joniburn/raspi-musicbox/python-musicbox/musicbox/score.py

# スコアファイル

import re
from datetime import datetime, timedelta
from typing import List, Tuple

from musicbox.scale import PITCH_FREQ_MAP


def _is_comment_line(line: str) -> bool:
    """コメント行であればTrueを返す。"""
    return line.startswith('#')


class ScoreParseError(Exception):
    """スコアファイルのパース失敗エラー"""
    def __init__(self, msg):
        super().__init__(msg)


class Note:
    """音階や長さを持った1つの音"""

    def __init__(self, note_line: str):
        cmd_args = re.split('[ ]+', note_line)
        self.pitch = cmd_args[0]       # 音階
        self.step = int(cmd_args[1])   # 音長基準(何分音符か)
        self.nstep = int(cmd_args[2])  # 音長(step何個分か)
        if len(cmd_args) <= 3:
            self.duration = 100        # 音の伸ばし率(何%まで伸ばすか)
        else:
            self.duration = int(cmd_args[3])
        if self.duration <= 0 or self.duration > 100:
            raise ScoreParseError(f'duration value should be in range '
                                  f'(0, 100]: {self.duration}')

    def to_timeline(self, bar: float, t: datetime):
        if self.pitch == 'x':
            freq = 0  # 休符
        else:
            freq = PITCH_FREQ_MAP[self.pitch]

        notelen = bar / self.step
        # N倍する前に、マイクロ秒以下を切り捨てる
        # このようにしないと、"x 16 1"を10行分と"x 8 5"を1行分にずれが生じる
        notelen = int(notelen * 1000000) / 1000000.0
        notelen = notelen * self.nstep

        if self.duration == 100:
            return [(freq, t + timedelta(seconds=notelen))]
        else:
            timeline = []
            notelen_on = notelen * self.duration / 100
            timeline.append((freq, t + timedelta(seconds=notelen_on)))
            timeline.append((0, t + timedelta(seconds=notelen)))
            return timeline


class ScoreBlock:
    """一定のBPMを持ったスコアのブロック"""

    def __init__(self, lines: List[str], ntrack: int):
        self._bpm = 0
        self._tracks = []
        for i in range(0, ntrack):
            self._tracks.append([])
        self._parse(lines)

    def _parse(self, lines: List[str]):
        for lnum, line in enumerate(lines):
            # 1行目はbpm行 "@ bpm XXX"
            if lnum == 0:
                self._parse_bpm(line)
                continue

            # コメント行と空行はスキップ
            if _is_comment_line(line) or not line:
                continue

            # 各トラックをパース
            track_lines = line.split(',')
            for i in range(0, len(self._tracks)):
                if len(track_lines) > i:
                    track_line = track_lines[i]
                else:
                    track_line = ''
                track_line = track_line.strip()
                if track_line:
                    self._tracks[i].append(Note(track_line))

    def _parse_bpm(self, bpm_line: str):
        bpm_line = bpm_line.split(',', maxsplit=1)[0]
        bpm_line_args = bpm_line.split(' ')
        if bpm_line_args[1] != 'bpm':
            raise ScoreParseError('no bpm line is provided at beggining '
                                  'of score block.')
        self._bpm = int(bpm_line_args[2])

    def build_timeline(self, start: datetime, track: int) \
            -> List[Tuple[float, datetime]]:
        # bpmから各音符の長さを計算
        bar = 60.0 / self._bpm * 4  # 1小節の長さ。4分音符はこの長さの1/4, ...

        timeline = []
        cur = start
        for note in self._tracks[track]:
            items = note.to_timeline(bar, cur)
            timeline.extend(items)
            cur = items[-1][1]
        return timeline


class TrackProperties:
    """トラック毎のプロパティ"""

    def __init__(self, mode='tone', duty=None):
        self.mode = mode
        self.duty = duty


class Score:
    """スコアファイルのパース結果を保持するクラス"""

    def __init__(self, fname):
        self.ntrack = 0
        self._track_props = []
        self._score_blocks = []
        self._parse(fname)

    def _parse(self, fname):
        # プロパティセクションとスコア本体の行を読み込む
        prop_lines = []
        score_blocks = []
        with open(fname) as f:
            # プロパティセクション
            for line in f:
                line = line.strip()
                if line.startswith('@'):
                    score_blocks.append([line])
                    break
                prop_lines.append(line)

            # スコア本体
            current_block_lines = score_blocks[0]
            for line in f:
                line = line.strip()
                if line.startswith('@'):
                    next_block_lines = [line]
                    score_blocks.append(next_block_lines)
                    current_block_lines = next_block_lines
                    continue
                current_block_lines.append(line)

        # プロパティのパース
        for l in prop_lines:
            self._parse_prop_line(l)
        if not self.ntrack:
            raise ScoreParseError('no ntrack is provided.')

        # スコア本体のパース
        self._score_blocks = [ScoreBlock(lines, self.ntrack)
                              for lines in score_blocks]

    def _parse_prop_line(self, line: str):
        line = line.split(',', maxsplit=1)[0]
        if _is_comment_line(line):
            return

        cmd_args = line.split(' ')
        if cmd_args[0] == 'ntrack':
            self.ntrack = int(cmd_args[1])
            for i in range(0, self.ntrack):
                self._track_props.append(TrackProperties())
        elif cmd_args[0] == 'track':
            track_num = int(cmd_args[1])
            key, val = cmd_args[2].split('=', maxsplit=1)
            if key == 'mode':
                self._track_props[track_num - 1].mode = val
            if key == 'duty':
                self._track_props[track_num - 1].duty = int(val)

    def prop(self, track: int):
        return self._track_props[track]

    def build_timeline(self, track: int):
        timeline = []
        starttime = datetime.now()

        for block in self._score_blocks:
            newtimeline = block.build_timeline(starttime, track)
            timeline.extend(newtimeline)
            if len(newtimeline) == 0:
                break
            starttime = newtimeline[-1][1]
        return timeline
