joniburn/raspi-musicbox/gpiosound/optparse.h

#ifndef OPTPARSE_H__
#define OPTPARSE_H__

enum sound_mode {
  SOUND_MODE_UNKNOWN,
  SOUND_MODE_TONE,
  SOUND_MODE_NOISE,
};

// コマンドライン引数のパース結果を格納する構造体
typedef struct {
  enum sound_mode mode;
  int outpin;
  unsigned char dutyratio;
} options;

/**
 * コマンドライン引数をパースする。
 *
 * 引数に不備がある場合はエラーを出力してプログラムを終了する。
 *
 * @param argc mainに渡されるargc
 * @param argv mainに渡されるargv
 * @param opt  パース結果の格納先
 */
extern void parse_args(int argc, char **argv, options *opt);

#endif /* OPTPARSE_H__ */
