joniburn/raspi-musicbox/python-musicbox/musicbox/scale.py

from typing import Dict


# 平均律音階 ( http://nvc.webcrow.jp/TR4.HTM より)
PITCH_FREQ_MAP: Dict[str, float] = {
  '1c':  65.40637983,
  '1c+': 69.29564594,
  '1d':  73.41617986,
  '1d+': 77.78173351,
  '1e':  82.4068765,
  '1f':  87.30704484,
  '1f+': 92.49859238,
  '1g':  97.99884543,
  '1g+': 103.8261606,
  '1a':  109.9999859,
  '1a+': 116.5409261,
  '1b':  123.4708109,
  '2c':  130.812768,
  '2c+': 138.5913007,
  '2d':  146.8323691,
  '2d+': 155.563477,
  '2e':  164.8137635,
  '2f':  174.6141008,
  '2f+': 184.9971966,
  '2g':  195.9977034,
  '2g+': 207.6523344,
  '2a':  219.9999859,
  '2a+': 233.0818671,
  '2b':  246.9416375,
  '3c':  261.6255528,
  '3c+': 277.1826192,
  '3d':  293.664757,
  '3d+': 311.1269738,
  '3e':  329.6275481,
  '3f':  349.228224,
  '3f+': 369.9944168,
  '3g':  391.9954318,
  '3g+': 415.3046954,
  '3a':  440.0,
  '3a+': 466.163764,
  '3b':  493.8833065,
  '4c':  523.251139,
  '4c+': 554.3652738,
  '4d':  587.3295515,
  '4d+': 622.2539873,
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
}
"""音階名と周波数のマップ"""
